LukevLuijn/robox/robox_models/segment_00/linear_motion/pulley_spacer.stl

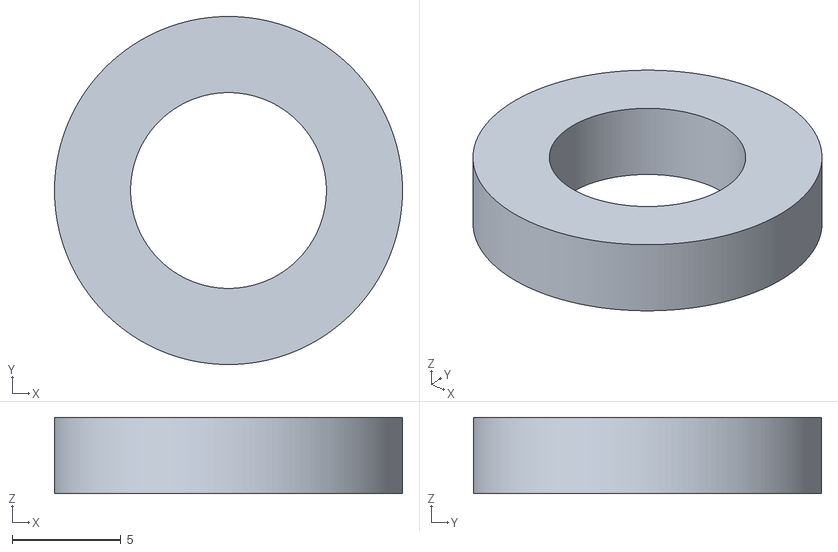
[picture p23: CAD file, 2022-05-27]
robox_models/segment_00/linear_motion/pulley_spacer.stl
16.0 x 16.0 x 3.50
