LukevLuijn/robox/robox_models/segment_00/main_controller/frame_pcb_spacer.stl

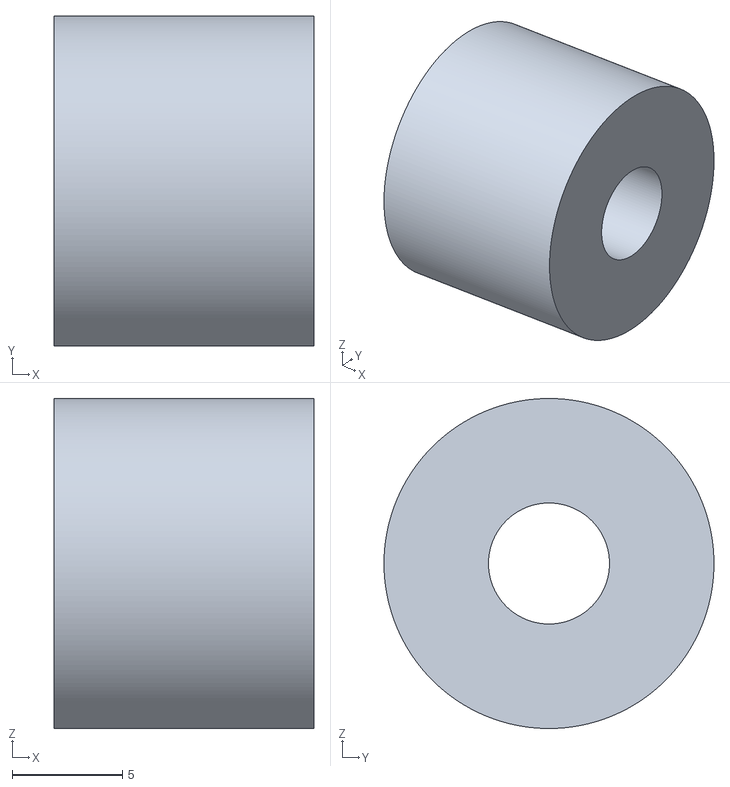
[picture p24: CAD file, 2022-05-27]
robox_models/segment_00/main_controller/frame_pcb_spacer.stl
11.8 x 15.0 x 15.0
