LukevLuijn/robox/robox_models/segment_00/outer_panels/panel_sub_bracket.stl

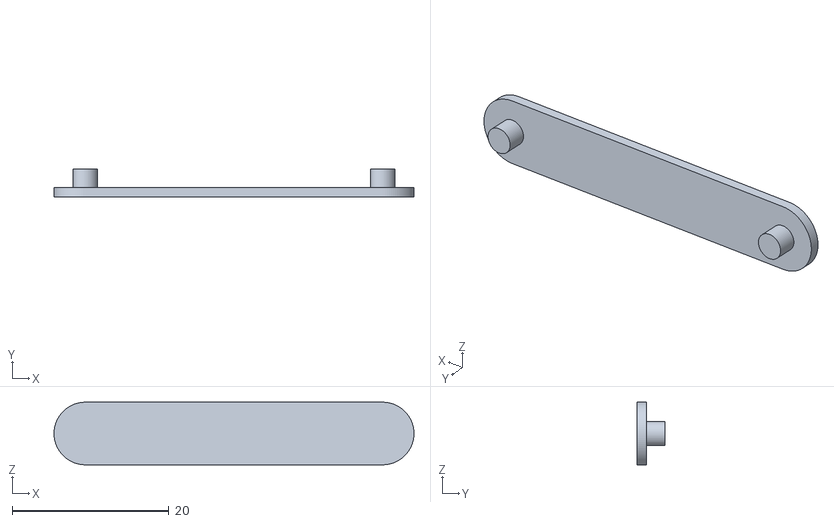
[picture p25: CAD file, 2022-05-27]
robox_models/segment_00/outer_panels/panel_sub_bracket.stl
46.0 x 3.60 x 8.00
