LukevLuijn/robox/robox_models/segment_01/accent_pieces/01 (3).stl

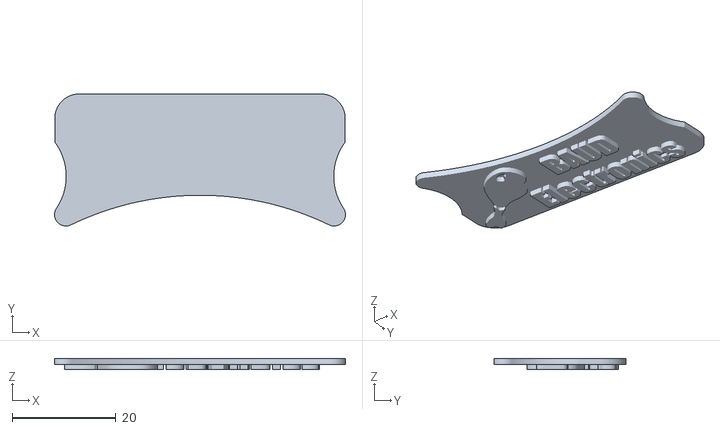
[picture p26: CAD file, 2022-05-27]
robox_models/segment_01/accent_pieces/01 (3).stl
56.1 x 25.5 x 2.20
