LukevLuijn/robox/robox_models/segment_01/main_part/body_mid_mid.stl

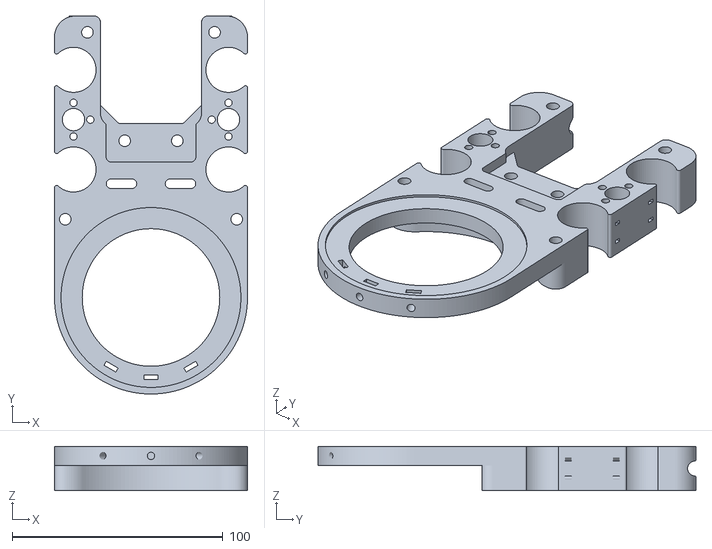
[picture p27: CAD file, 2022-05-27]
robox_models/segment_01/main_part/body_mid_mid.stl
91.7 x 179.5 x 21.0
