LukevLuijn/robox/robox_models/segment_02/accent_pieces/02 (0).stl

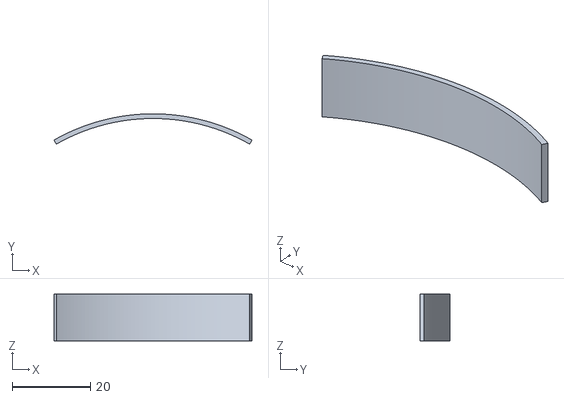
[picture p28: CAD file, 2022-05-27]
robox_models/segment_02/accent_pieces/02 (0).stl
50.6 x 7.75 x 11.9
