LukevLuijn/robox/robox_models/segment_02/main_part/body_mid.stl

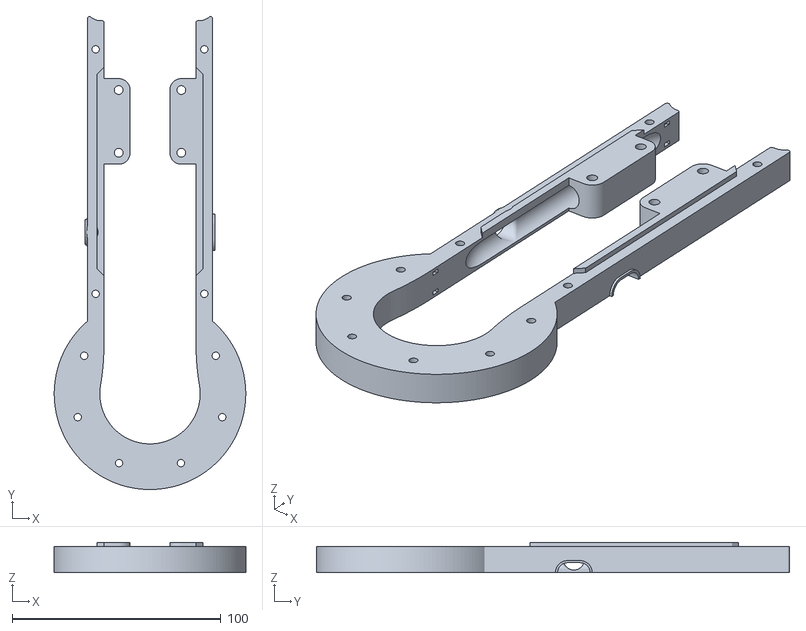
[picture p29: CAD file, 2022-05-27]
robox_models/segment_02/main_part/body_mid.stl
91.7 x 226.3 x 14.5
