LukevLuijn/robox/robox_models/gripper/magnet_bracket.stl

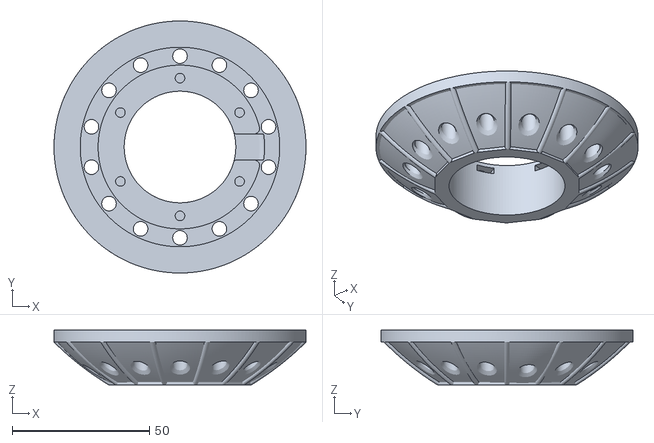
[picture p31: CAD file, 2022-05-27]
robox_models/gripper/magnet_bracket.stl
91.7 x 91.7 x 20.0
