LukevLuijn/robox/robox_models/segment_00/accent_pieces/logo_bone.stl

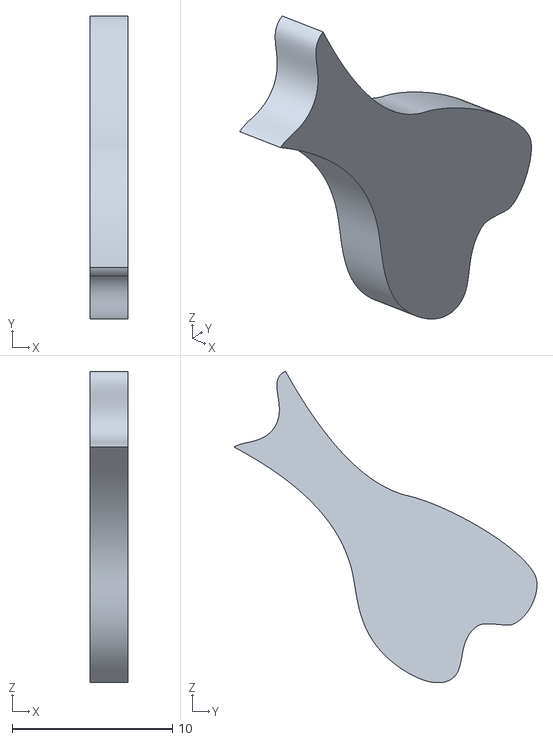
[picture p32: CAD file, 2022-05-27]
robox_models/segment_00/accent_pieces/logo_bone.stl
2.40 x 18.9 x 19.4
