LukevLuijn/robox/robox_models/segment_00/electronics_housing/back_cover_03.stl

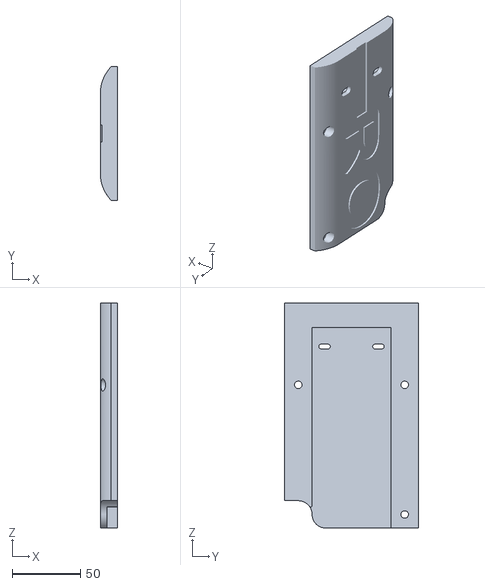
[picture p33: CAD file, 2022-05-27]
robox_models/segment_00/electronics_housing/back_cover_03.stl
12.8 x 98.0 x 164.9
