LukevLuijn/robox/robox_models/segment_00/linear_motion/bot_holder_mid.stl

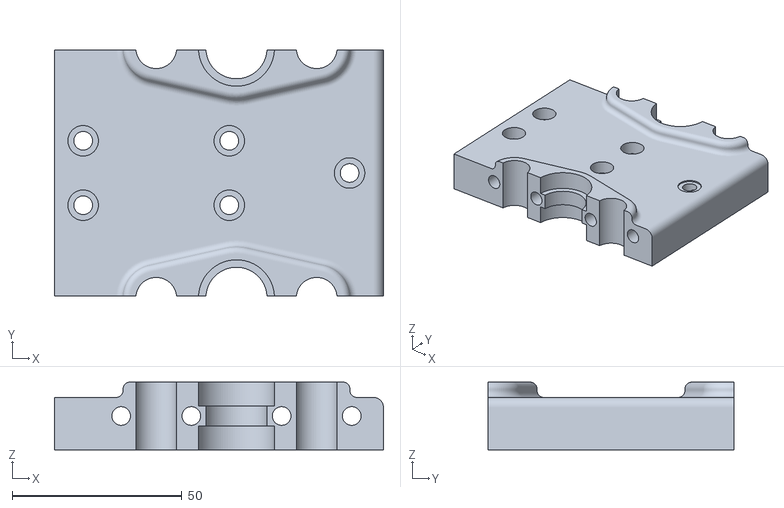
[picture p34: CAD file, 2022-05-27]
robox_models/segment_00/linear_motion/bot_holder_mid.stl
97.0 x 72.6 x 20.0
