LukevLuijn/robox/robox_models/segment_00/main_controller/pcb_pcb_spacer.stl

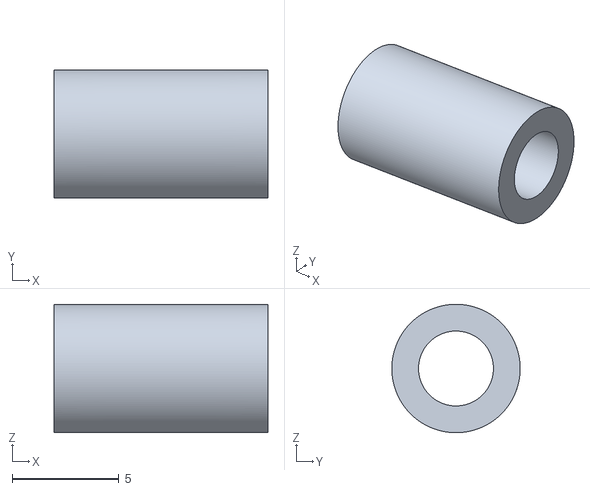
[picture p35: CAD file, 2022-05-27]
robox_models/segment_00/main_controller/pcb_pcb_spacer.stl
10.0 x 6.00 x 6.00
