LukevLuijn/robox/robox_models/segment_00/outer_panels/top_bracket.stl

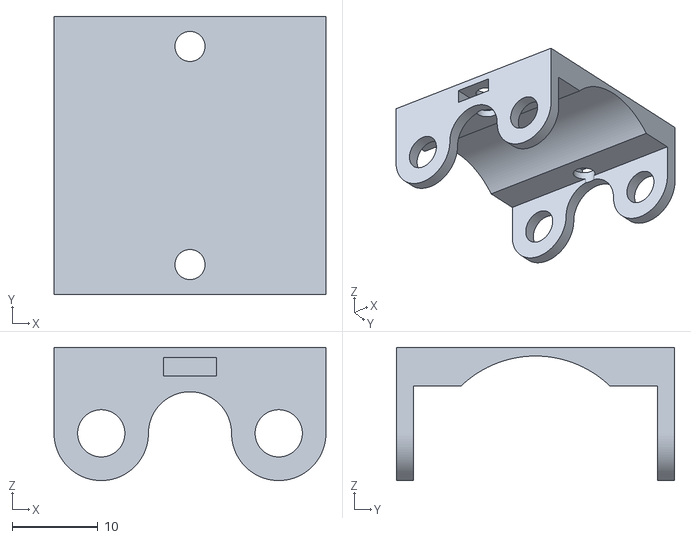
[picture p36: CAD file, 2022-05-27]
robox_models/segment_00/outer_panels/top_bracket.stl
31.7 x 32.4 x 15.5
