LukevLuijn/robox/robox_models/segment_01/accent_pieces/01 (2).stl

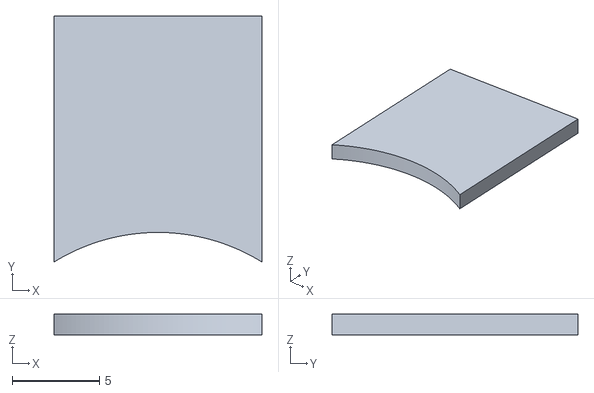
[picture p37: CAD file, 2022-05-27]
robox_models/segment_01/accent_pieces/01 (2).stl
11.9 x 14.1 x 1.20
