LukevLuijn/robox/robox_models/segment_01/main_part/pulley_top.stl

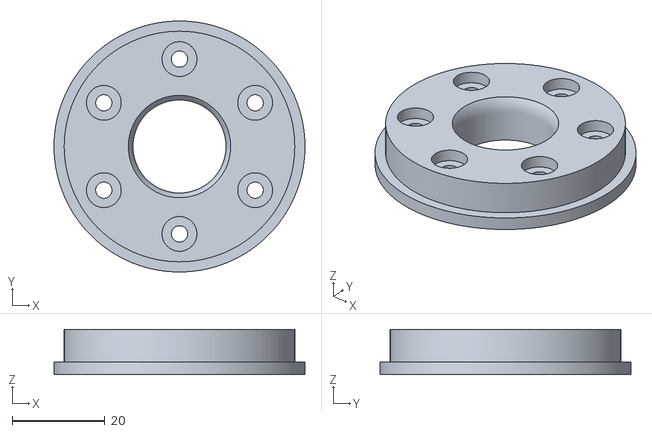
[picture p38: CAD file, 2022-05-27]
robox_models/segment_01/main_part/pulley_top.stl
54.0 x 54.0 x 9.75
