LukevLuijn/robox/robox_models/segment_02/accent_pieces/02 (3).stl

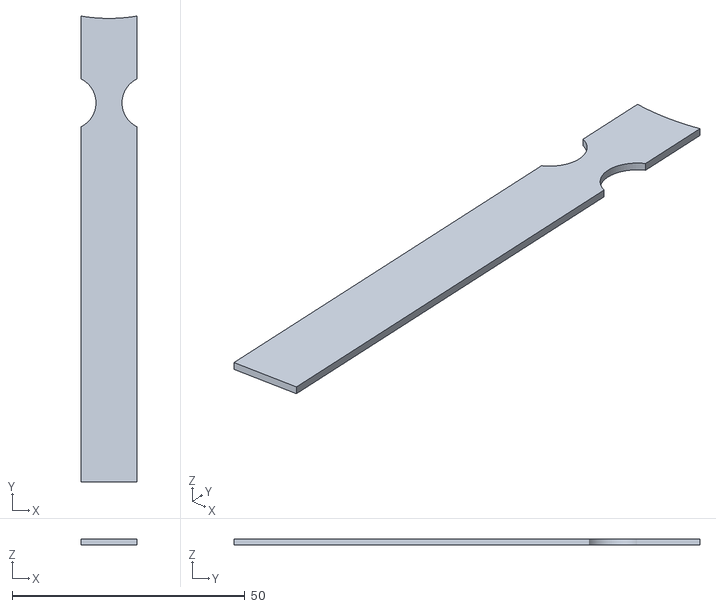
[picture p39: CAD file, 2022-05-27]
robox_models/segment_02/accent_pieces/02 (3).stl
12.1 x 100.1 x 1.20
