LukevLuijn/robox/robox_models/segment_02/main_part/body_bot.stl

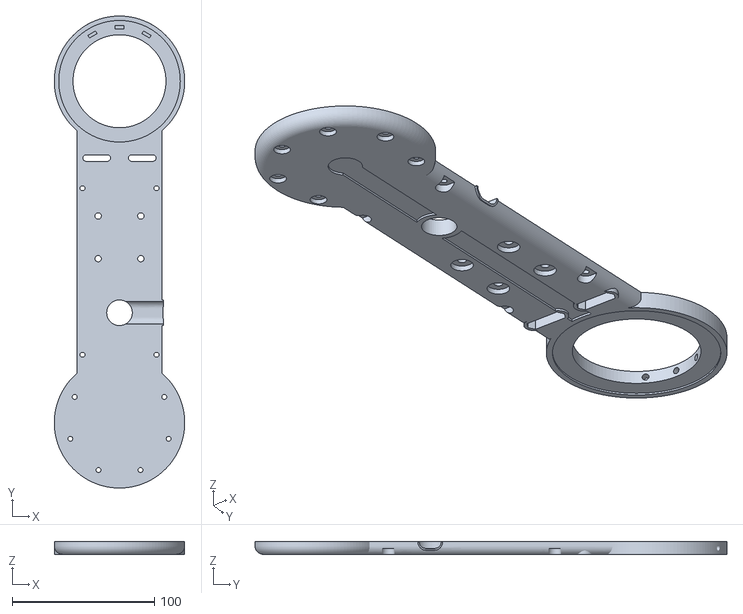
[picture p40: CAD file, 2022-05-27]
robox_models/segment_02/main_part/body_bot.stl
91.7 x 331.7 x 9.00
