LukevLuijn/robox/robox_models/segment_03/accent_pieces/03 (1).stl

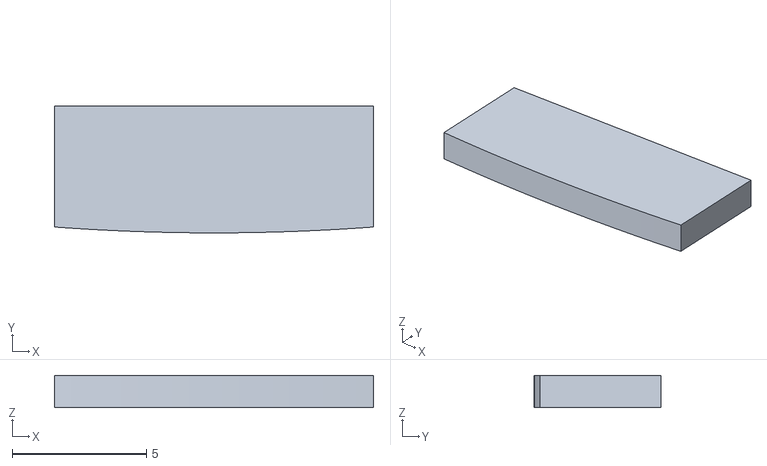
[picture p41: CAD file, 2022-05-27]
robox_models/segment_03/accent_pieces/03 (1).stl
11.9 x 4.73 x 1.20
