LukevLuijn/robox/robox_models/segment_03/main_part/bumper_front_v2.stl

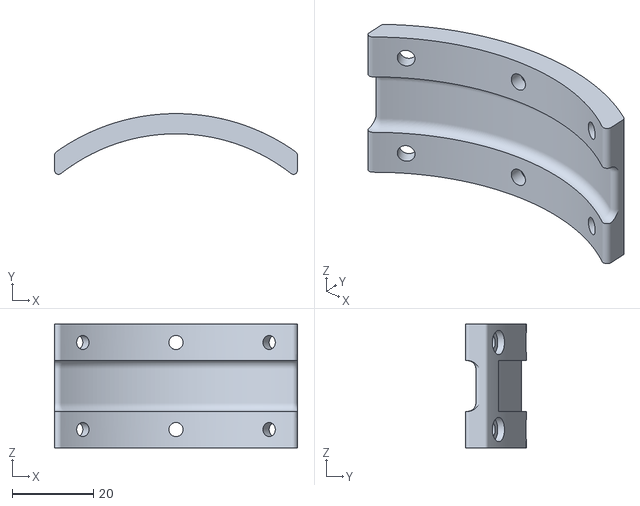
[picture p42: CAD file, 2022-05-27]
robox_models/segment_03/main_part/bumper_front_v2.stl
60.0 x 15.0 x 30.5
