LukevLuijn/robox/robox_models/segment_00/accent_pieces/00 (0).stl

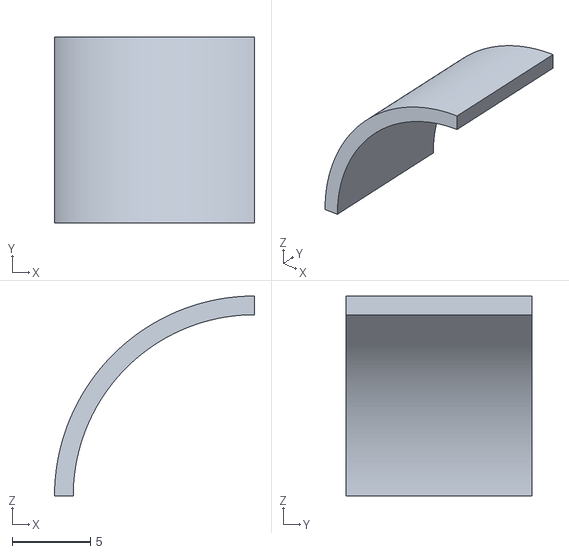
[picture p43: CAD file, 2022-05-27]
robox_models/segment_00/accent_pieces/00 (0).stl
12.8 x 11.9 x 12.8
