LukevLuijn/robox/robox_models/segment_00/electronics_housing/stepper_driver_bracket.stl

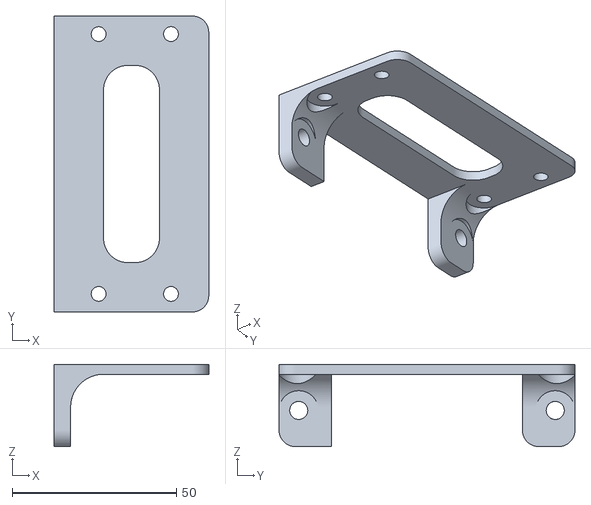
[picture p44: CAD file, 2022-05-27]
robox_models/segment_00/electronics_housing/stepper_driver_bracket.stl
47.0 x 90.0 x 25.0
