LukevLuijn/robox/robox_models/segment_00/linear_motion/top_holder_left.stl

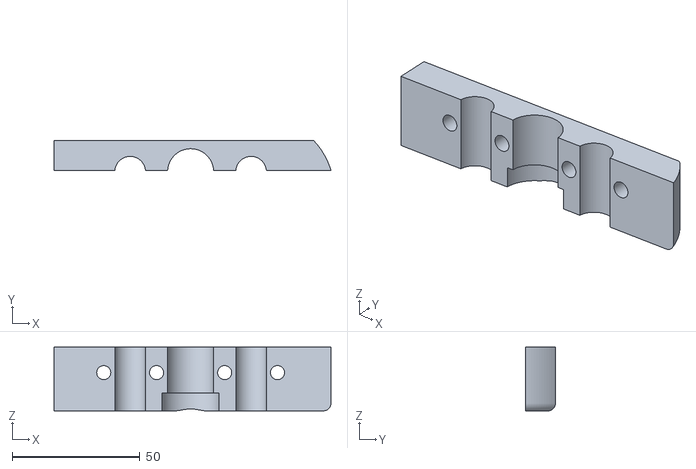
[picture p45: CAD file, 2022-05-27]
robox_models/segment_00/linear_motion/top_holder_left.stl
108.4 x 11.7 x 25.0
