LukevLuijn/robox/robox_models/segment_00/main_controller/motor_controller_bot.stl

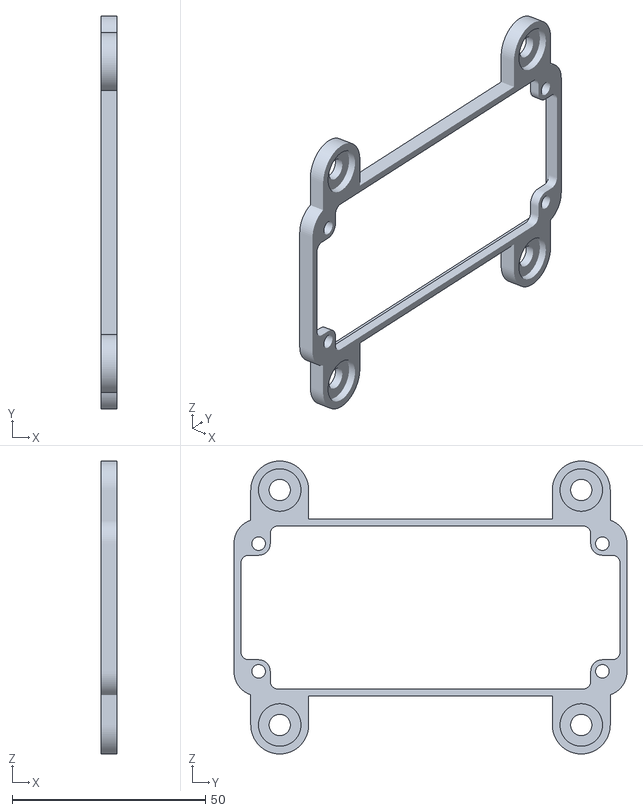
[picture p46: CAD file, 2022-05-27]
robox_models/segment_00/main_controller/motor_controller_bot.stl
4.10 x 101.7 x 75.8
