LukevLuijn/robox/robox_models/segment_00/outer_panels/panel_bracket.stl

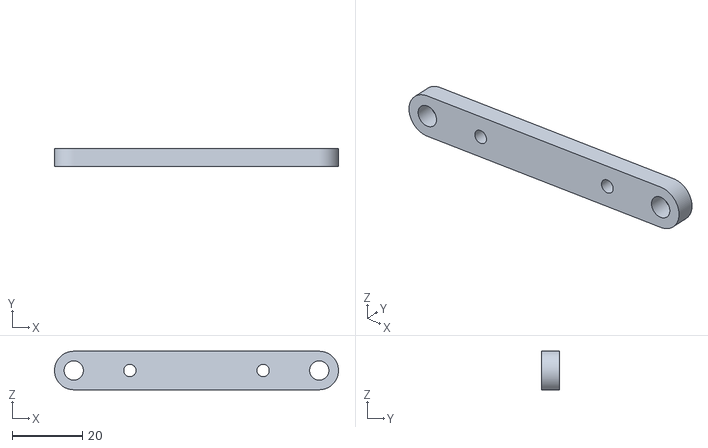
[picture p47: CAD file, 2022-05-27]
robox_models/segment_00/outer_panels/panel_bracket.stl
81.0 x 5.00 x 11.0
