LukevLuijn/robox/robox_models/segment_01/accent_pieces/01 (0).stl

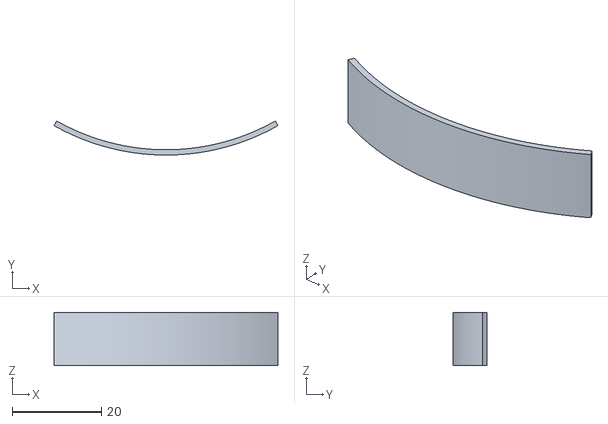
[picture p48: CAD file, 2022-05-27]
robox_models/segment_01/accent_pieces/01 (0).stl
50.3 x 7.66 x 11.9
