LukevLuijn/robox/robox_models/segment_01/main_part/body_bot_mid.stl

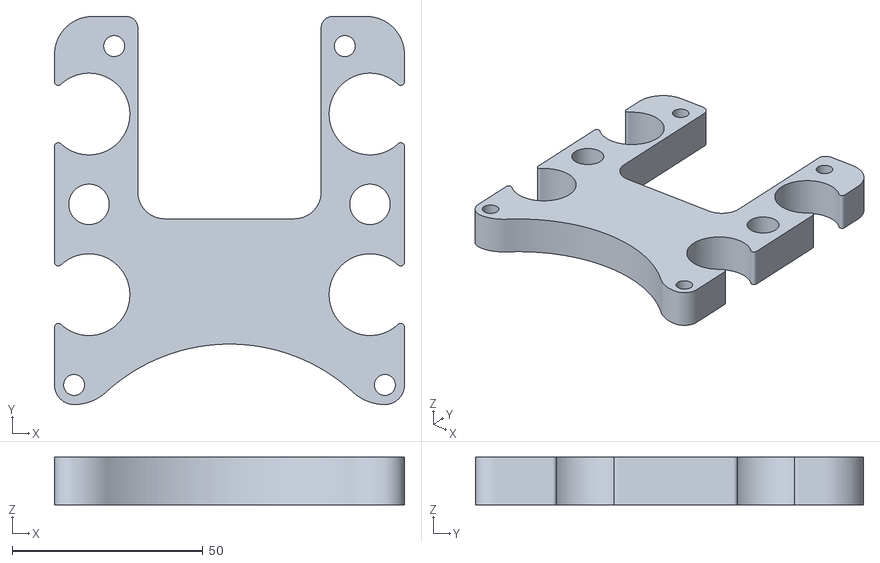
[picture p49: CAD file, 2022-05-27]
robox_models/segment_01/main_part/body_bot_mid.stl
91.7 x 101.7 x 12.5
