LukevLuijn/robox/robox_models/segment_02/accent_pieces/02 (2).stl

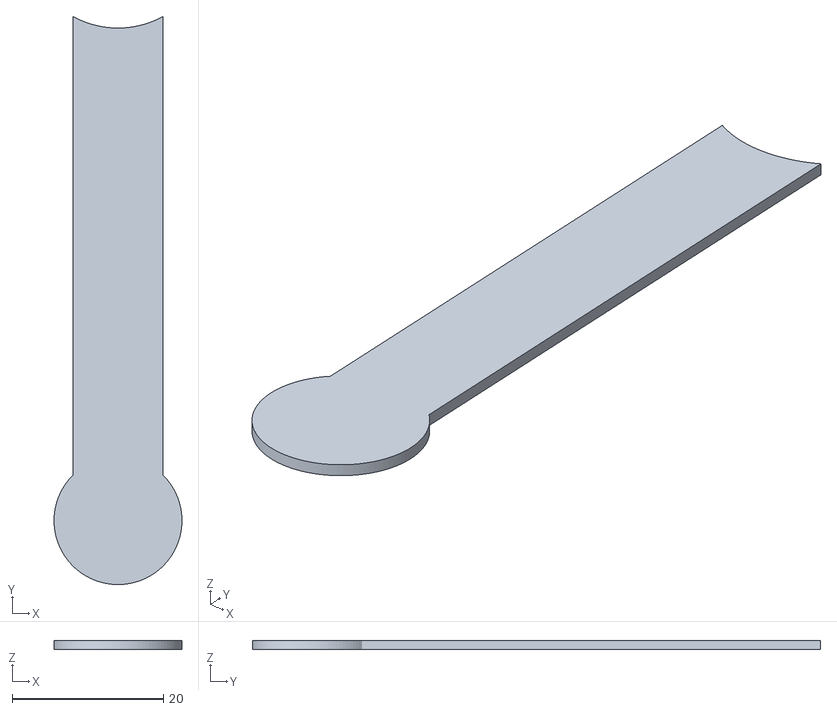
[picture p50: CAD file, 2022-05-27]
robox_models/segment_02/accent_pieces/02 (2).stl
16.9 x 75.0 x 1.20
