LukevLuijn/robox/robox_models/segment_02/main_part/pulley_top.stl

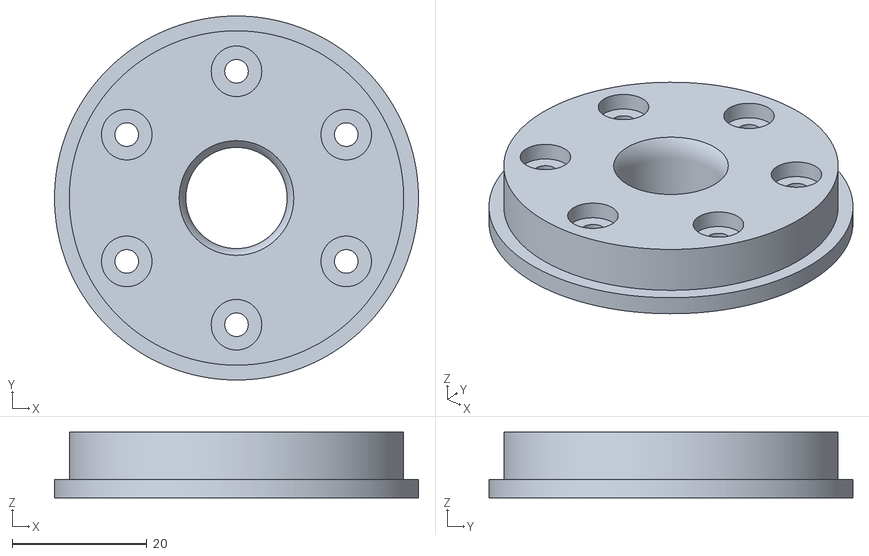
[picture p51: CAD file, 2022-05-27]
robox_models/segment_02/main_part/pulley_top.stl
54.0 x 54.0 x 9.75
