LukevLuijn/robox/robox_models/segment_03/accent_pieces/03 (0).stl

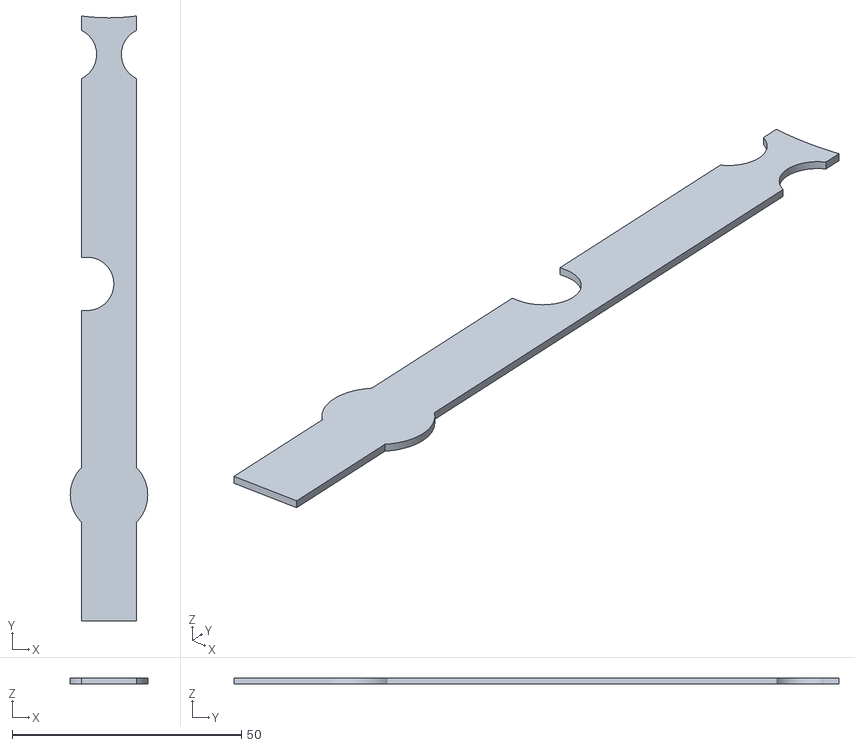
[picture p52: CAD file, 2022-05-27]
robox_models/segment_03/accent_pieces/03 (0).stl
16.9 x 131.9 x 1.20
