LukevLuijn/robox/robox_models/segment_00/accent_pieces/title_R.stl

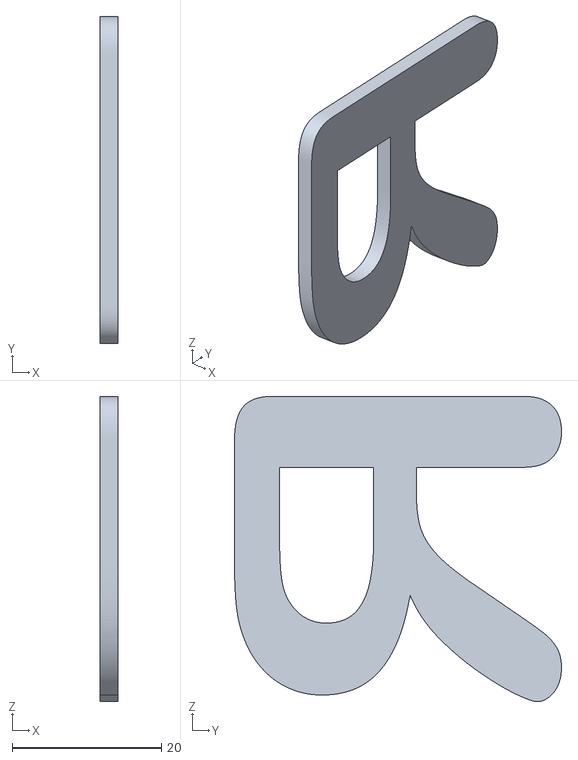
[picture p53: CAD file, 2022-05-27]
robox_models/segment_00/accent_pieces/title_R.stl
2.40 x 43.8 x 40.9
