LukevLuijn/robox/robox_models/segment_00/linear_motion/top_holder_mid.stl

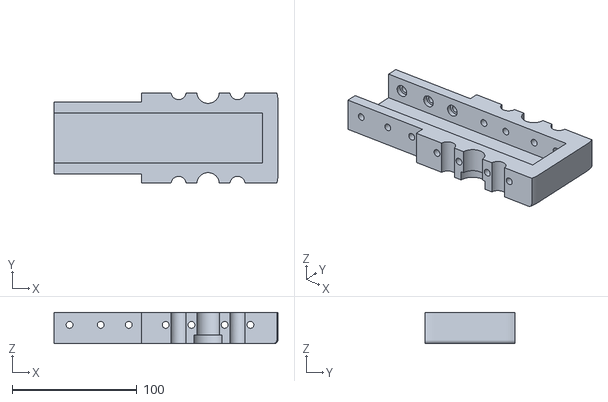
[picture p54: CAD file, 2022-05-27]
robox_models/segment_00/linear_motion/top_holder_mid.stl
179.8 x 72.6 x 25.0
