LukevLuijn/robox/robox_models/segment_00/outer_panels/panel_bot.stl

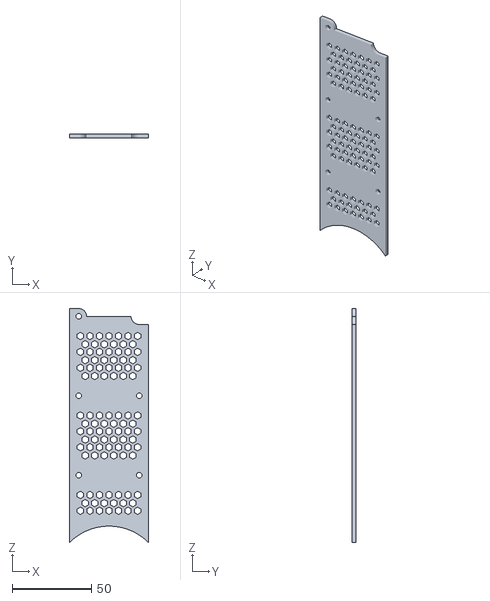
[picture p55: CAD file, 2022-05-27]
robox_models/segment_00/outer_panels/panel_bot.stl
49.6 x 2.40 x 147.3
