LukevLuijn/robox/robox_models/segment_03/accent_pieces/03 (2).stl

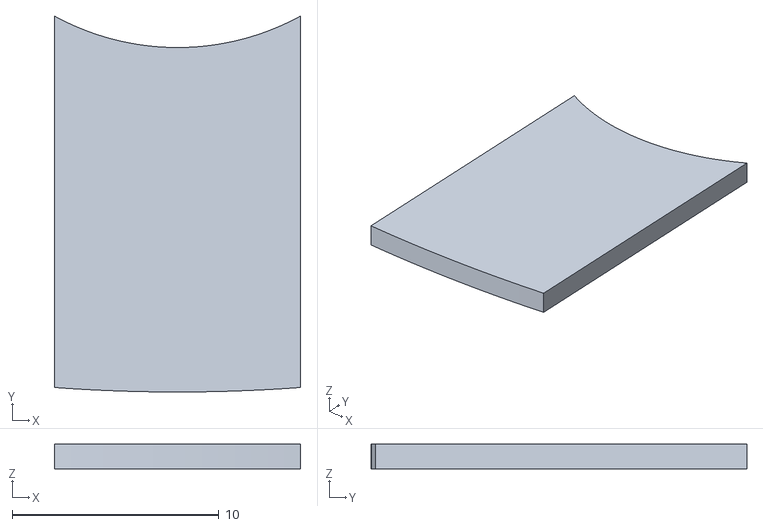
[picture p56: CAD file, 2022-05-27]
robox_models/segment_03/accent_pieces/03 (2).stl
11.9 x 18.2 x 1.20
