LukevLuijn/robox/robox_models/segment_03/main_part/body_top.stl

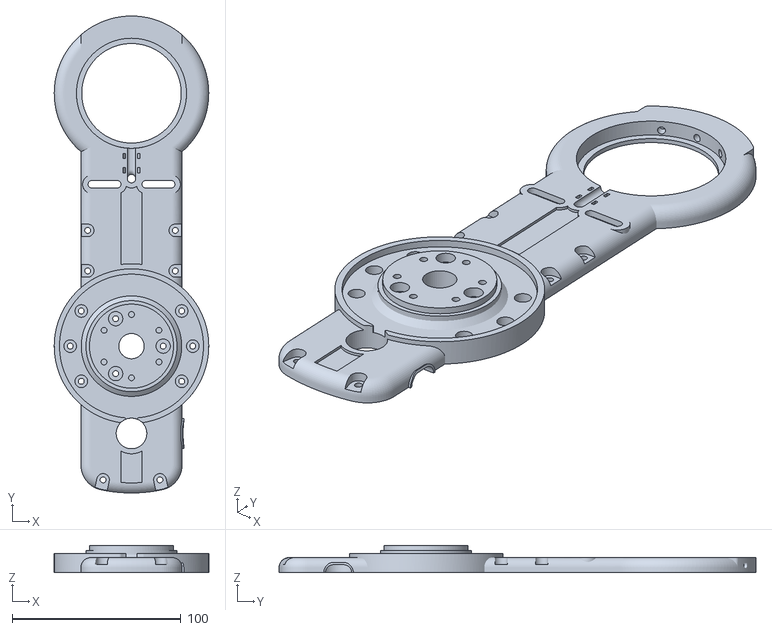
[picture p57: CAD file, 2022-05-27]
robox_models/segment_03/main_part/body_top.stl
91.7 x 282.9 x 16.2
