LukevLuijn/robox/robox_models/segment_00/accent_pieces/title_X.stl

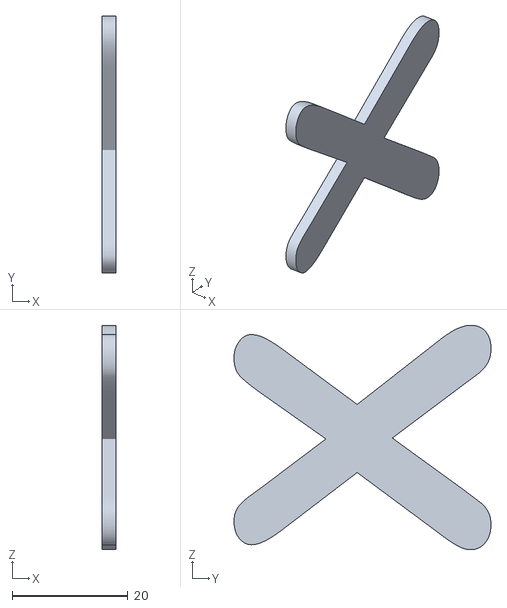
[picture p58: CAD file, 2022-05-27]
robox_models/segment_00/accent_pieces/title_X.stl
2.40 x 44.5 x 38.9
