LukevLuijn/robox/robox_models/segment_00/electronics_housing/motor_connector_bracket.stl

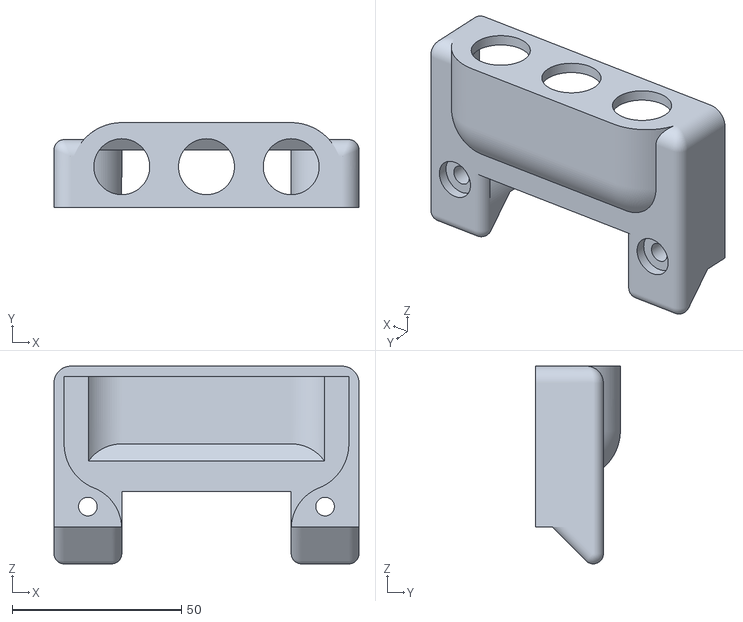
[picture p59: CAD file, 2022-05-27]
robox_models/segment_00/electronics_housing/motor_connector_bracket.stl
90.0 x 25.0 x 58.4
