LukevLuijn/robox/robox_models/segment_00/outer_panels/top_cover.stl

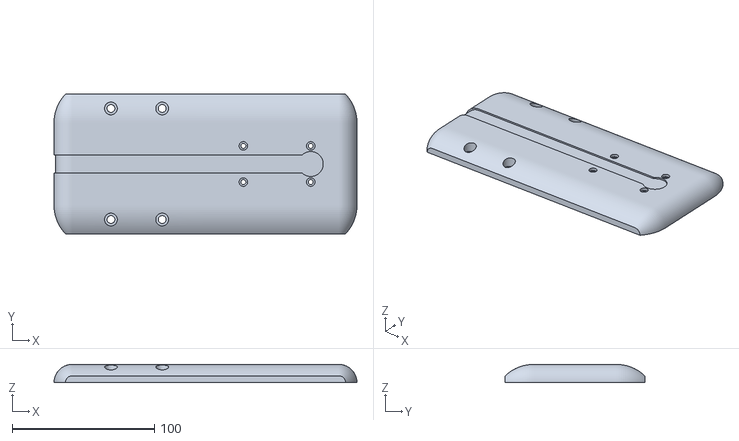
[picture p60: CAD file, 2022-05-27]
robox_models/segment_00/outer_panels/top_cover.stl
212.8 x 98.0 x 12.8
