LukevLuijn/robox/robox_models/segment_01/main_part/body_top_mid.stl

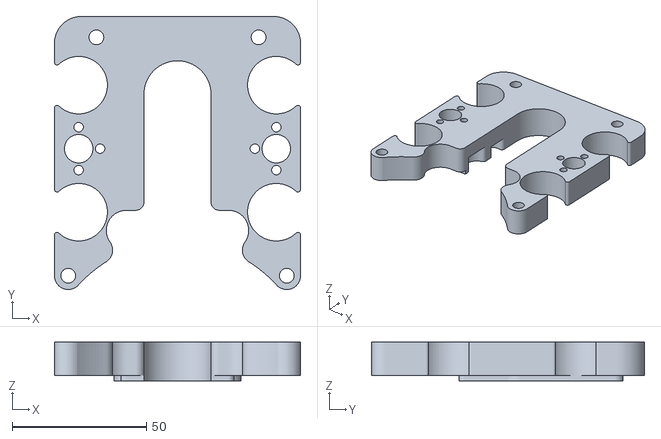
[picture p61: CAD file, 2022-05-27]
robox_models/segment_01/main_part/body_top_mid.stl
91.7 x 101.7 x 14.5
