LukevLuijn/robox/robox_models/segment_02/main_part/body_top.stl

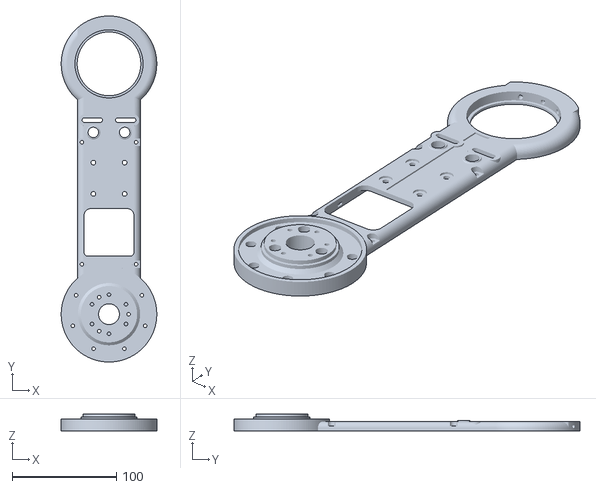
[picture p62: CAD file, 2022-05-27]
robox_models/segment_02/main_part/body_top.stl
91.7 x 331.7 x 16.2
