LukevLuijn/robox/robox_models/segment_00/accent_pieces/00 (1).stl

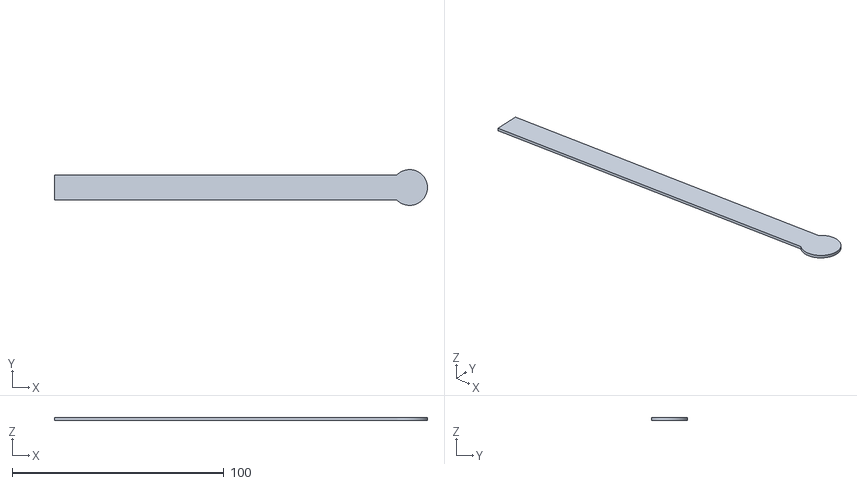
[picture p64: CAD file, 2022-05-27]
robox_models/segment_00/accent_pieces/00 (1).stl
176.0 x 16.9 x 1.20
