LukevLuijn/robox/robox_models/segment_00/linear_motion/sensor_bracket.stl

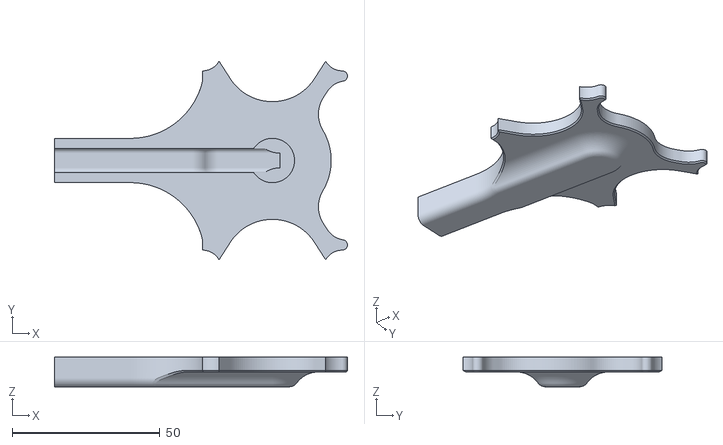
[picture p65: CAD file, 2022-05-27]
robox_models/segment_00/linear_motion/sensor_bracket.stl
99.1 x 67.1 x 10.0
