LukevLuijn/robox/robox_models/segment_01/main_part/body_bot.stl

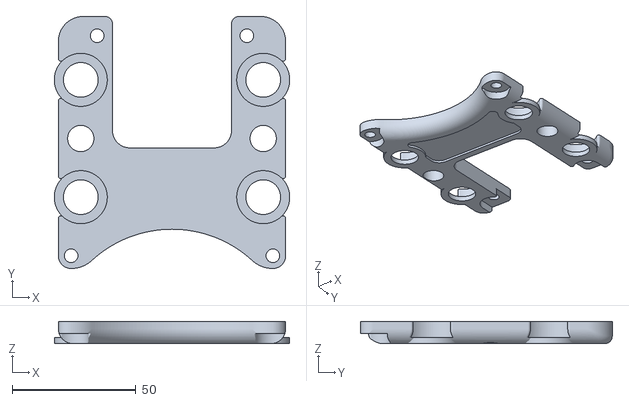
[picture p66: CAD file, 2022-05-27]
robox_models/segment_01/main_part/body_bot.stl
95.0 x 101.7 x 9.00
