LukevLuijn/robox/robox_models/segment_00/electronics_housing/buck_converter_bracket.stl

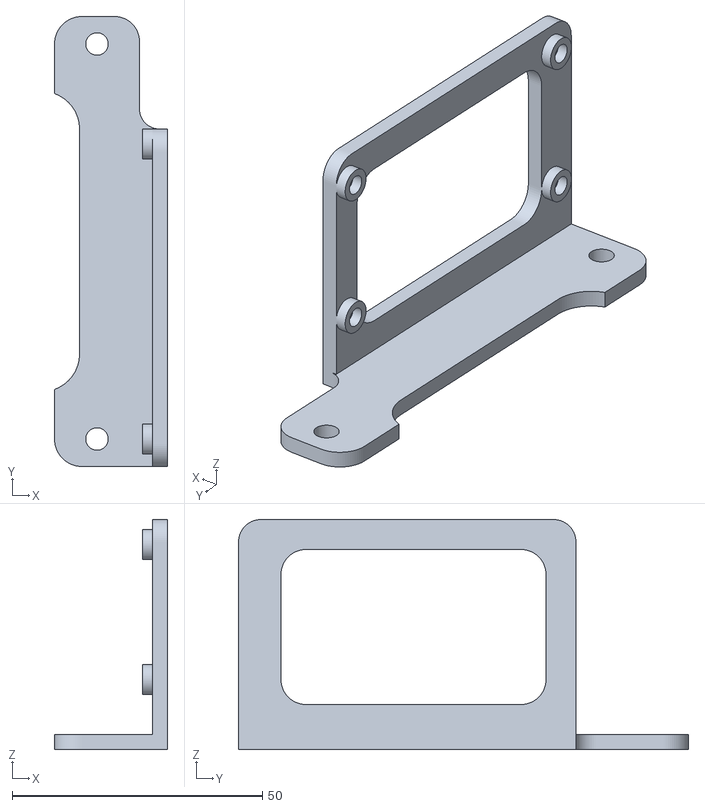
[picture p68: CAD file, 2022-05-27]
robox_models/segment_00/electronics_housing/buck_converter_bracket.stl
22.6 x 90.0 x 46.0
