LukevLuijn/robox/robox_models/segment_00/linear_motion/bot_holder_bracket.stl

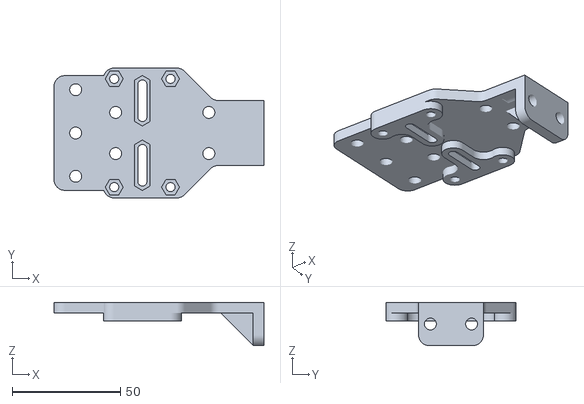
[picture p69: CAD file, 2022-05-27]
robox_models/segment_00/linear_motion/bot_holder_bracket.stl
97.0 x 60.0 x 20.0
