LukevLuijn/robox/robox_control_ui/include/config/global_config.h

// ======================================
// Filename:    global_config.h
// Project:     ROBOX Control UI
// Author:      Luke van Luijn
// Data:        15-05-2022
// ======================================

#ifndef ROBOX_CONTROL_UI_GLOBAL_CONFIG_H
#define ROBOX_CONTROL_UI_GLOBAL_CONFIG_H

#define WINDOW_WIDTH 920
#define WINDOW_HEIGHT 700
#define WINDOW_TITLE "ROBOX - Control UI"

#define REQUEST_START_CHAR '<'
#define REQUEST_STOP_CHAR '>'

#define RESPONSE_START_CHAR '#'
#define RESPONSE_STOP_CHAR '*'

#define LOG_START_CHAR '@'
#define LOG_STOP_CHAR '*'
#define LOG_PART_SEPARATOR ';'

#define WRITE_DELAY_US 150

#define RUN_TIME_DATA_UPDATE_DELAY_MS 100

#define ASSETS_PATH "../assets/png/"

#endif//ROBOX_CONTROL_UI_GLOBAL_CONFIG_H
